es-ude/ElasticNodeHardware/spice/mosfetTest.asc

M1: nmos; NTLMS4504N
M2: pmos
R1: res; 1
R2: res; 100
R3: res; 1
R4: res; 100
U1: DMP2008UFG
V1: voltage; 0
V2: voltage; 3.3
Named nets: 0, Vinput, vdd, vinput, vo, vo2
.dc V2 0 3.3 .01
